topi314/Gopher-Satellite/config/common/koala-base.yaml

substitutions:
  # Phases of the Voice Assistant
  # The voice assistant is ready to be triggered by a wake word
  voice_assist_idle_phase_id: '1'
  # The voice assistant is waiting for a voice command (after being triggered by the wake word)
  voice_assist_waiting_for_command_phase_id: '2'
  # The voice assistant is listening for a voice command
  voice_assist_listening_for_command_phase_id: '3'
  # The voice assistant is currently processing the command
  voice_assist_thinking_phase_id: '4'
  # The voice assistant is replying to the command
  voice_assist_replying_phase_id: '5'
  # The voice assistant is not ready
  voice_assist_not_ready_phase_id: '10'
  # The voice assistant encountered an error
  voice_assist_error_phase_id: '11'

esphome:
  project: 
    name: formatbce.Koala Satellite
    version: 2025.1.3
  name: koala-satellite
  friendly_name: Koala Satellite
  name_add_mac_suffix: true
  min_version: 2024.12.2
  platformio_options:
    board_build.flash_mode: dio
  on_boot:
    priority: 375
    then:
      - sensor.template.publish:
          id: next_timer
          state: -1
      # Run the script to refresh the LED status
      - script.execute: control_leds
      # If after 10 minutes, the device is still initializing (It did not yet connect to Home Assistant), turn off the init_in_progress variable and run the script to refresh the LED status
      - delay: 10min
      - if:
          condition:
            lambda: return id(init_in_progress);
          then:
            - lambda: id(init_in_progress) = false;
            - script.execute: control_leds
  on_shutdown:
    then:
      # Prevent loud noise on software restart
      - lambda: id(respeaker).mute_speaker();

esp32:
  board: esp32-s3-devkitc-1
  variant: esp32s3
  flash_size: 16MB
  framework:
    type: esp-idf
    version: recommended
    sdkconfig_options:
      CONFIG_ESP32S3_DEFAULT_CPU_FREQ_240: "y"
      CONFIG_ESP32S3_DATA_CACHE_64KB: "y"
      CONFIG_ESP32S3_DATA_CACHE_LINE_64B: "y"
      CONFIG_ESP32S3_INSTRUCTION_CACHE_32KB: "y"
      CONFIG_ESP32_S3_BOX_BOARD: "y"
      CONFIG_SPIRAM_ALLOW_STACK_EXTERNAL_MEMORY: "y"

      CONFIG_SPIRAM_TRY_ALLOCATE_WIFI_LWIP: "y"

      # Settings based on https://github.com/espressif/esp-adf/issues/297#issuecomment-783811702
      CONFIG_ESP32_WIFI_STATIC_RX_BUFFER_NUM: "16"
      CONFIG_ESP32_WIFI_DYNAMIC_RX_BUFFER_NUM: "512"
      CONFIG_ESP32_WIFI_STATIC_TX_BUFFER: "y"
      CONFIG_ESP32_WIFI_TX_BUFFER_TYPE: "0"
      CONFIG_ESP32_WIFI_STATIC_TX_BUFFER_NUM: "8"
      CONFIG_ESP32_WIFI_CACHE_TX_BUFFER_NUM: "32"
      CONFIG_ESP32_WIFI_AMPDU_TX_ENABLED: "y"
      CONFIG_ESP32_WIFI_TX_BA_WIN: "16"
      CONFIG_ESP32_WIFI_AMPDU_RX_ENABLED: "y"
      CONFIG_ESP32_WIFI_RX_BA_WIN: "32"
      CONFIG_LWIP_MAX_ACTIVE_TCP: "16"
      CONFIG_LWIP_MAX_LISTENING_TCP: "16"
      CONFIG_TCP_MAXRTX: "12"
      CONFIG_TCP_SYNMAXRTX: "6"
      CONFIG_TCP_MSS: "1436"
      CONFIG_TCP_MSL: "60000"
      CONFIG_TCP_SND_BUF_DEFAULT: "65535"
      CONFIG_TCP_WND_DEFAULT: "65535"  # Adjusted from linked settings to avoid compilation error
      CONFIG_TCP_RECVMBOX_SIZE: "512"
      CONFIG_TCP_QUEUE_OOSEQ: "y"
      CONFIG_TCP_OVERSIZE_MSS: "y"
      CONFIG_LWIP_WND_SCALE: "y"
      CONFIG_TCP_RCV_SCALE: "3"
      CONFIG_LWIP_TCPIP_RECVMBOX_SIZE: "512"

      CONFIG_BT_ALLOCATION_FROM_SPIRAM_FIRST: "y"
      CONFIG_BT_BLE_DYNAMIC_ENV_MEMORY: "y"

      CONFIG_MBEDTLS_EXTERNAL_MEM_ALLOC: "y"
      CONFIG_MBEDTLS_SSL_PROTO_TLS1_3: "y"  # TLS1.3 support isn't enabled by default in IDF 5.1.5

wifi:
  id: wifi_id
  on_connect:
    - lambda: id(improv_ble_in_progress) = false;
    - script.execute: control_leds
  on_disconnect:
    - script.execute: control_leds

logger:
  level: DEBUG
  logs:
    sensor: WARN  # avoids logging debug sensor updates

api:
  id: api_id
  actions:
    - action: start_va
      then:
        - voice_assistant.start
    - action: stop_va
      then:
        - voice_assistant.stop
  on_client_connected:
    - script.execute: control_leds
  on_client_disconnected:
    - script.execute: control_leds

# Uncomment this, if you have problems with text-to-speech because of Home Assistant HTTPS internal URL
# http_request:
#   verify_ssl: false

ota:
  - platform: esphome
    id: ota_esphome

i2c:
  - id: internal_i2c
    sda: GPIO5
    scl: GPIO6
    frequency: 400kHz

psram:
  mode: octal
  speed: 80MHz

globals:
  # Global index for our LEDs. So that switching between different animation does not lead to unwanted effects.
  - id: global_led_animation_index
    type: int
    restore_value: no
    initial_value: '0'
  # Global initialization variable. Initialized to true and set to false once everything is connected. Only used to have a smooth "plugging" experience
  - id: init_in_progress
    type: bool
    restore_value: no
    initial_value: 'true'
  # Global variable storing the state of ImprovBLE. Used to draw different LED animations
  - id: improv_ble_in_progress
    type: bool
    restore_value: no
    initial_value: 'false'
  # Global variable tracking the phase of the voice assistant (defined above). Initialized to not_ready
  - id: voice_assistant_phase
    type: int
    restore_value: no
    initial_value: ${voice_assist_not_ready_phase_id}
  # Global variable tracking if the dial was recently touched.
  - id: dial_touched
    type: bool
    restore_value: no
    initial_value: 'false'
  # Global variable tracking if the LED color was recently changed.
  - id: color_changed
    type: bool
    restore_value: no
    initial_value: 'false'
  # Global variable storing the first active timer
  - id: first_active_timer
    type: voice_assistant::Timer
    restore_value: false
  # Global variable storing if a timer is active
  - id: is_timer_active
    type: bool
    restore_value: false
  # Global variable storing if a factory reset was requested. If it is set to true, the device will factory reset once the center button is released
  - id: factory_reset_requested
    type: bool
    restore_value: no
    initial_value: 'false'

switch:
  # Hardware speaker mute
  - platform: template
    id: speaker_mute_switch
    name: Speaker mute
    icon: mdi:volume-mute
    internal: true
    optimistic: true
    turn_on_action:
      - lambda: id(respeaker).mute_speaker();
    turn_off_action:
      - lambda: id(respeaker).unmute_speaker();
  # stateless momentary mic mute switch
  - platform: gpio
    internal: true
    pin: 
      number: GPIO4 # D3
      inverted: true
    id: mute_toggle
    on_turn_on:
      - delay: 300ms
      - switch.turn_off: mute_toggle
  # stateful user facing mic mute switch
  - platform: template
    id: mic_mute_switch
    name: Mic mute
    icon: mdi:microphone-off
    lambda: |-
      if (id(mute_state).state) {
        return true;
      } else {
        return false;
      }
    on_turn_on:
      - if:
          condition:
            and:
              - lambda: return !id(init_in_progress);
              - switch.is_on: mute_sound
          then:
            - script.execute:
                id: play_sound
                priority: false
                sound_file: !lambda return id(mute_switch_on_sound);
    on_turn_off:
      - if:
          condition:
            and:
              - lambda: return !id(init_in_progress);
              - switch.is_on: mute_sound
          then:
            - script.execute:
                id: play_sound
                priority: false
                sound_file: !lambda return id(mute_switch_off_sound);
    turn_on_action:
      - switch.turn_on: mute_toggle
    turn_off_action:
      - switch.turn_on: mute_toggle
  # Button click Sounds Switch.
  - platform: template
    id: button_sound
    name: Button click sounds
    icon: "mdi:bullhorn"
    entity_category: config
    optimistic: true
    restore_mode: RESTORE_DEFAULT_ON
  # Mute Sound Switch.
  - platform: template
    id: mute_sound
    name: Mute/unmute sound
    icon: "mdi:bullhorn"
    entity_category: config
    optimistic: true
    restore_mode: RESTORE_DEFAULT_ON
  # Wake Word Sound Switch.
  - platform: template
    id: wake_sound
    name: Wake sound
    icon: "mdi:bullhorn"
    entity_category: config
    optimistic: true
    restore_mode: RESTORE_DEFAULT_ON
  # Internal switch to track when a timer is ringing on the device.
  - platform: template
    id: timer_ringing
    optimistic: true
    internal: true
    restore_mode: ALWAYS_OFF
    on_turn_off:
      # Disable stop wake word
      - lambda: id(stop).disable();
      # Stop any current annoucement (ie: stop the timer ring mid playback)
      - if:
          condition:
            lambda: return id(nabu_media_player)->state == media_player::MediaPlayerState::MEDIA_PLAYER_STATE_ANNOUNCING;
          then:
            lambda: |-
              id(nabu_media_player)
                ->make_call()
                .set_command(media_player::MediaPlayerCommand::MEDIA_PLAYER_COMMAND_STOP)
                .set_announcement(true)
                .perform();
      # Set back ducking ratio to zero
      - nabu.set_ducking:
          decibel_reduction: 0
          duration: 1.0s
      # Refresh the LED ring
      - script.execute: control_leds
    on_turn_on:
      # Duck audio
      - nabu.set_ducking:
          decibel_reduction: 20
          duration: 0.0s
      # Enable stop wake word
      - lambda: id(stop).enable();
      # Ring timer
      - script.execute: ring_timer
      # Refresh LED
      - script.execute: control_leds
      # If 15 minutes have passed and the timer is still ringing, stop it.
      - delay: 15min
      - switch.turn_off: timer_ringing

binary_sensor:
  # User Button. Used for many things (See on_multi_click)
  - platform: gpio
    id: user_button
    pin:
      number: GPIO42
      inverted: true
    name: "User button"
    on_press:
      - script.execute: control_leds
    on_release:
      - script.execute: control_leds
      # If a factory reset is requested, factory reset on release
      - if:
          condition:
            lambda: return id(factory_reset_requested);
          then:
            - button.press: factory_reset_button
    on_multi_click:
      # Simple Click:
      #   - Abort "things" in order
      #     - Timer
      #     - Announcements
      #     - Voice Assistant Pipeline run
      #     - Music
      #   - Starts the voice assistant if it is not yet running and if the device is not muted.
      - timing:
          - ON for at most 1s
          - OFF for at least 0.25s
        then:
          - if:
              condition:
                lambda: return !id(init_in_progress) && !id(color_changed);
              then:
                - if:
                    condition:
                      switch.is_on: timer_ringing
                    then:
                      - switch.turn_off: timer_ringing
                    else:
                      - if:
                          condition:
                            lambda: return id(nabu_media_player)->state == media_player::MediaPlayerState::MEDIA_PLAYER_STATE_ANNOUNCING;
                          then:
                            - lambda: |
                                id(nabu_media_player)
                                  ->make_call()
                                  .set_command(media_player::MediaPlayerCommand::MEDIA_PLAYER_COMMAND_STOP)
                                  .set_announcement(true)
                                  .perform();
                          else:
                            - if:
                                condition:
                                  voice_assistant.is_running:
                                then:
                                  - voice_assistant.stop:
                                else:
                                  - if:
                                      condition:
                                        media_player.is_playing:
                                      then:
                                        - media_player.pause:
                                      else:
                                        - if:
                                            condition:
                                              and:
                                                - switch.is_off: mic_mute_switch
                                                - not:
                                                    voice_assistant.is_running
                                            then:
                                              - if:
                                                  condition:
                                                    switch.is_on: button_sound
                                                  then:
                                                    - script.execute:
                                                        id: play_sound
                                                        priority: true
                                                        sound_file: !lambda return id(center_button_press_sound);
                                                    - delay: 300ms
                                              - voice_assistant.start:
      # Double Click
      #  . Exposed as an event entity. To be used in automations inside Home Assistant
      - timing:
          - ON for at most 1s
          - OFF for at most 0.25s
          - ON for at most 1s
          - OFF for at least 0.25s
        then:
          - if:
              condition:
                lambda: return !id(init_in_progress) && !id(color_changed);
              then:
                - if:
                    condition:
                      switch.is_on: button_sound
                    then:
                      - script.execute:
                          id: play_sound
                          priority: false
                          sound_file: !lambda return id(center_button_double_press_sound);
                - event.trigger:
                    id: button_press_event
                    event_type: "double_press"
      # Triple Click
      #  . Exposed as an event entity. To be used in automations inside Home Assistant
      - timing:
          - ON for at most 1s
          - OFF for at most 0.25s
          - ON for at most 1s
          - OFF for at most 0.25s
          - ON for at most 1s
          - OFF for at least 0.25s
        then:
          - if:
              condition:
                lambda: return !id(init_in_progress) && !id(color_changed);
              then:
                - if:
                    condition:
                      switch.is_on: button_sound
                    then:
                      - script.execute:
                          id: play_sound
                          priority: false
                          sound_file: !lambda return id(center_button_triple_press_sound);
                - event.trigger:
                    id: button_press_event
                    event_type: "triple_press"
      # Long Press
      #  . Exposed as an event entity. To be used in automations inside Home Assistant
      - timing:
          - ON for at least 1s
        then:
          - if:
              condition:
                lambda: return !id(init_in_progress) && !id(color_changed);
              then:
                - if:
                    condition:
                      switch.is_on: button_sound
                    then:
                      - script.execute:
                          id: play_sound
                          priority: false
                          sound_file: !lambda return id(center_button_long_press_sound);
                - light.turn_off: voice_assistant_leds
                - event.trigger:
                    id: button_press_event
                    event_type: "long_press"
      # Factory Reset Warning
      #  . Audible and Visible warning.
      - timing:
          - ON for at least 10s
        then:
          - if:
              condition:
                lambda: return !id(dial_touched);
              then:
                - light.turn_on:
                    brightness: 100%
                    id: voice_assistant_leds
                    effect: "Factory Reset Coming Up"
                - script.execute:
                    id: play_sound
                    priority: true
                    sound_file: !lambda return id(factory_reset_initiated_sound);
                - wait_until:
                    binary_sensor.is_off: user_button
                - if:
                    condition:
                      lambda: return !id(factory_reset_requested);
                    then:
                      - light.turn_off: voice_assistant_leds
                      - script.execute:
                          id: play_sound
                          priority: true
                          sound_file: !lambda return id(factory_reset_cancelled_sound);
      # Factory Reset Confirmed.
      #  . Audible warning to prompt user to release the button
      #  . Set factory_reset_requested to true
      - timing:
          - ON for at least 22s
        then:
          - if:
              condition:
                lambda: return !id(dial_touched);
              then:
                - script.execute:
                    id: play_sound
                    priority: true
                    sound_file: !lambda return id(factory_reset_confirmed_sound);
                - light.turn_on:
                    brightness: 100%
                    red: 100%
                    green: 0%
                    blue: 0%
                    id: voice_assistant_leds
                    effect: "none"
                - lambda: id(factory_reset_requested) = true;

  - platform: gpio
  # this thing is pretty flaky, giving several on/off commands at once. Do not use it for serious stuff
    id: rotary_button
    disabled_by_default: true
    pin:
      number: GPIO20
      inverted: true
      mode:
        input: true
        pullup: true

light:
  # Hardware LED ring. Not used because remapping needed
  - platform: esp32_rmt_led_strip
    id: leds_internal
    pin: GPIO13
    rmt_channel: 1
    num_leds: 43
    rgb_order: GRB
    chipset: WS2812
    default_transition_length: 0ms

  # Voice Assistant LED ring. Remapping of the internal LED.
  # This light is not exposed. The device controls it
  - platform: partition
    id: voice_assistant_leds
    internal: true
    default_transition_length: 0ms
    segments:
      - id: leds_internal
        from: 0
        to: 31
        reversed: True
      - id: leds_internal
        from: 32
        to: 42
        reversed: True
    effects:
      - addressable_lambda:
          name: "Waiting for Command"
          update_interval: 100ms
          lambda: |-
            auto light_color = id(led_ring).current_values;
            Color color(light_color.get_red() * 255, light_color.get_green() * 255,
                  light_color.get_blue() * 255);
            for (int i = 0; i < 43; i++) {
              if (i % 6 == id(global_led_animation_index) % 6) {
                it[i] = color;
              } else if ((i + 5) % 6 == id(global_led_animation_index) % 6) {
                it[i] = color * 192;
              } else if ((i + 4) % 6 == id(global_led_animation_index) % 6) {
                it[i] = color * 128;
              } else {
                it[i] = Color::BLACK;
              }
            }
            id(global_led_animation_index) = (id(global_led_animation_index) + 1) % 43;
      - addressable_lambda:
          name: "Listening For Command"
          update_interval: 50ms
          lambda: |-
            auto light_color = id(led_ring).current_values;
            Color color(light_color.get_red() * 255, light_color.get_green() * 255, light_color.get_blue() * 255);
            for (int i = 0; i < 43; i++) {
              if (i % 6 == id(global_led_animation_index) % 6) {
                it[i] = color;
              } else if ((i + 5) % 6 == id(global_led_animation_index) % 6) {
                it[i] = color * 192;
              } else if ((i + 4) % 6 == id(global_led_animation_index) % 6) {
                it[i] = color * 128;
              } else {
                it[i] = Color::BLACK;
              }
            }
            id(global_led_animation_index) = (id(global_led_animation_index) + 1) % 43;
      - addressable_lambda:
          name: "Thinking"
          update_interval: 10ms
          lambda: |-
            static uint8_t brightness_step = 0;
            static bool brightness_decreasing = true;
            static uint8_t brightness_step_number = 10;
            if (initial_run) {
              brightness_step = 0;
              brightness_decreasing = true;
            }
            auto light_color = id(led_ring).current_values;
            Color color(light_color.get_red() * 255, light_color.get_green() * 255, light_color.get_blue() * 255);
            for (int i = 0; i < 43; i++) {
              if (i % 6 == id(global_led_animation_index) % 6) {
                it[i] = color * uint8_t(255/brightness_step_number*(brightness_step_number-brightness_step));
              } else {
                it[i] = Color::BLACK;
              }
            }
            if (brightness_decreasing) {
              brightness_step++;
            } else {
              brightness_step--;
            }
            if (brightness_step == 0 || brightness_step == brightness_step_number) {
              brightness_decreasing = !brightness_decreasing;
            }
      - addressable_lambda:
          name: "Replying"
          update_interval: 50ms
          lambda: |-
            id(global_led_animation_index) = (43 + id(global_led_animation_index) - 1) % 43;
            auto light_color = id(led_ring).current_values;
            Color color(light_color.get_red() * 255, light_color.get_green() * 255, light_color.get_blue() * 255);
            for (int i = 0; i < 43; i++) {
              if (i % 6 == id(global_led_animation_index) % 6) {
                it[i] = color;
              } else if ((i + 1) % 6 == id(global_led_animation_index) % 6) {
                it[i] = color * 192;
              } else if ((i + 2) % 6 == id(global_led_animation_index) % 6) {
                it[i] = color * 128;
              } else {
                it[i] = Color::BLACK;
              }
            }
      - addressable_lambda:
          name: "Volume Display"
          update_interval: 50ms
          lambda: |-
            Color color(255, 0, 255);
            Color silenced_color(255, 0, 0);
            auto volume_ratio = id(nabu_media_player).volume * 10.0f;
            auto is_muted = id(nabu_media_player).is_muted() || id(nabu_media_player).volume == 0.0f;
            for (int i = 0; i < 43; i++) {
              if (i <= volume_ratio && !is_muted) {
                it[i] = color * min( 255.0f * (volume_ratio - i) , 255.0f ) ;
              } else {
                it[i] = Color::BLACK;
              }
            }
            if (is_muted) {
              it[5] = silenced_color;
            }
      - addressable_lambda:
          name: "Center Button Touched"
          update_interval: 16ms
          lambda: |-
            if (initial_run) {
              // set voice_assistant_leds light to colors based on led_ring
              auto led_ring_cv = id(led_ring).current_values;
              auto va_leds_call = id(voice_assistant_leds).make_call();
              va_leds_call.from_light_color_values(led_ring_cv);
              va_leds_call.set_brightness( min ( max( id(led_ring).current_values.get_brightness() , 0.2f ) + 0.1f , 1.0f ) );
              va_leds_call.set_state(true);
              va_leds_call.perform();
            }
            auto light_color = id(voice_assistant_leds).current_values;
            Color color(light_color.get_red() * 255, light_color.get_green() * 255,
                  light_color.get_blue() * 255);
            for (int i = 0; i < 43; i++) {
              it[i] = color;
            }
      - addressable_twinkle:
          name: "Twinkle"
          twinkle_probability: 50%
      - addressable_rainbow:
          name: "Rainbow"
          width: 43
      - addressable_lambda:
          name: "Error"
          update_interval: 10ms
          lambda: |-
            static uint8_t brightness_step = 0;
            static bool brightness_decreasing = true;
            static uint8_t brightness_step_number = 10;
            if (initial_run) {
              brightness_step = 0;
              brightness_decreasing = true;
            }
            Color error_color(255, 0, 0);
            for (int i = 0; i < 43; i++) {
              it[i] = error_color * uint8_t(255/brightness_step_number*(brightness_step_number-brightness_step));
            }
            if (brightness_decreasing) {
              brightness_step++;
            } else {
              brightness_step--;
            }
            if (brightness_step == 0 || brightness_step == brightness_step_number) {
              brightness_decreasing = !brightness_decreasing;
            }
      - addressable_lambda:
          name: "Timer Ring"
          update_interval: 10ms
          lambda: |-
            static uint8_t brightness_step = 0;
            static bool brightness_decreasing = true;
            static uint8_t brightness_step_number = 10;
            if (initial_run) {
              brightness_step = 0;
              brightness_decreasing = true;
            }
            auto light_color = id(led_ring).current_values;
            Color color(light_color.get_red() * 255, light_color.get_green() * 255,
                  light_color.get_blue() * 255);
            for (int i = 0; i < 43; i++) {
              it[i] = color * uint8_t(255/brightness_step_number*(brightness_step_number-brightness_step));
            }
            if (brightness_decreasing) {
              brightness_step++;
            } else {
              brightness_step--;
            }
            if (brightness_step == 0 || brightness_step == brightness_step_number) {
              brightness_decreasing = !brightness_decreasing;
            }
      - addressable_lambda:
          name: "Timer Tick"
          update_interval: 100ms
          lambda: |-
            auto light_color = id(led_ring).current_values;
            Color color(light_color.get_red() * 255, light_color.get_green() * 255,
                  light_color.get_blue() * 255);
            auto timer_ratio = 43.0f * id(first_active_timer).seconds_left / max(id(first_active_timer).total_seconds , static_cast<uint32_t>(1));
            uint8_t last_led_on = static_cast<uint8_t>(ceil(timer_ratio)) - 1;
            for (int i = 0; i < 43; i++) {
              float brightness_dip = ( i == id(global_led_animation_index) % 43 && i != last_led_on ) ? 0.96f : 1.0f ;
              if (i <= timer_ratio) {
                it[i] = color * min(255.0f * brightness_dip * (timer_ratio - i) , 255.0f * brightness_dip) ;
              } else {
                it[i] = Color::BLACK;
              }
            }
            id(global_led_animation_index) = (43 + id(global_led_animation_index) - 1) % 43;
      - addressable_lambda:
          name: "Factory Reset Coming Up"
          update_interval: 1s
          lambda: |-
            static uint8_t index = 0;
            Color color(255, 0, 0);
            if (initial_run) {
              index = 0;
            }
            for (int i = 0; i < 43; i++) {
              if (i <= index ) {
                it[i] = color;
              } else {
                it[i] = Color::BLACK;
              }
            }
            index = (index + 1) % 43;
  # User facing LED ring. Remapping of the internal LEDs.
  # Exposed to be used by the user.
  - platform: partition
    id: led_ring
    name: LED Ring
    entity_category: config
    icon: "mdi:circle-outline"
    default_transition_length: 0ms
    restore_mode: RESTORE_DEFAULT_OFF
    initial_state:
      color_mode: rgb
      brightness: 66%
      red: 9.4%
      green: 73.3%
      blue: 94.9%
    segments:
      - id: leds_internal
        from: 0
        to: 31
        reversed: True
      - id: leds_internal
        from: 32
        to: 42
        reversed: True
    effects:
      - addressable_rainbow:
          name: "Rainbow"
          width: 43

  - platform: esp32_rmt_led_strip
    id: led_respeaker_onboard
    name: LED Respeaker onboard
    disabled_by_default: true
    internal: false
    rgb_order: GRB
    pin: GPIO1
    num_leds: 1
    rmt_channel: 2
    chipset: ws2812
    entity_category: config
    default_transition_length: 0s
    effects:
      - pulse:
          name: "Fast Pulse"
          transition_length: 100ms
          update_interval: 100ms
          min_brightness: 50%
          max_brightness: 100%
      - pulse:
          name: "Slow Pulse"
          transition_length: 500ms
          update_interval: 500ms
          min_brightness: 50%
          max_brightness: 100%
  - platform: esp32_rmt_led_strip
    id: led_esp_onboard
    name: LED ESP onboard
    disabled_by_default: true
    internal: false
    rgb_order: GRB
    pin: GPIO48
    num_leds: 1
    rmt_channel: 0
    chipset: ws2812
    entity_category: config
    default_transition_length: 0s

sensor:
  # The dial. Used to control volume and Hue of the LED ring.
  - platform: rotary_encoder
    id: dial
    pin_a: GPIO47
    pin_b: GPIO21
    resolution: 2
    on_clockwise:
      - lambda: id(dial_touched) = true;
      - if:
          condition:
            binary_sensor.is_off: user_button
          then:
            - script.execute:
                id: control_volume
                increase_volume: true
          else:
            - script.execute:
                id: control_hue
                increase_hue: true
    on_anticlockwise:
      - lambda: id(dial_touched) = true;
      - if:
          condition:
            binary_sensor.is_off: user_button
          then:
            - script.execute:
                id: control_volume
                increase_volume: false
          else:
            - script.execute:
                id: control_hue
                increase_hue: false
  - platform: template
    id: next_timer
    name: "Next timer"
    update_interval: never
    disabled_by_default: true
    device_class: duration
    unit_of_measurement: s
    icon: "mdi:timer"

text_sensor:
  - platform: template
    id: next_timer_name
    name: "Next timer name"
    icon: "mdi:timer"
    disabled_by_default: true
  - platform: template
    id: tts_uri
    name: "TTS URI"
    disabled_by_default: true

event:
  # Event entity exposed to the user to automate on complex center button presses.
  # The simple press is not exposed as it is used to control the device itself.
  - platform: template
    id: button_press_event
    name: "Button press"
    icon: mdi:button-pointer
    device_class: button
    event_types:
      - double_press
      - triple_press
      - long_press

script:
  # Master script controlling the LEDs, based on different conditions : initialization in progress, wifi and api connected and voice assistant phase.
  # For the sake of simplicity and re-usability, the script calls child scripts defined below.
  # This script will be called every time one of these conditions is changing.
  - id: control_leds
    then:
      - lambda: |
          id(check_if_timers_active).execute();
          if (id(is_timer_active)){
            id(fetch_first_active_timer).execute();
          }
          if (id(improv_ble_in_progress)) {
            id(control_leds_improv_ble_state).execute();
          } else if (id(init_in_progress)) {
            id(control_leds_init_state).execute();
          } else if (!id(wifi_id).is_connected() || !id(api_id).is_connected()){
            id(control_leds_no_ha_connection_state).execute();
          } else if (id(user_button).state) {
            id(control_leds_center_button_touched).execute();
          } else if (id(dial_touched)) {
            id(control_leds_volume_changed).execute();
          } else if (id(timer_ringing).state) {
            id(control_leds_timer_ringing).execute();
          } else if (id(voice_assistant_phase) == ${voice_assist_waiting_for_command_phase_id}) {
            id(control_leds_voice_assistant_waiting_for_command_phase).execute();
          } else if (id(voice_assistant_phase) == ${voice_assist_listening_for_command_phase_id}) {
            id(control_leds_voice_assistant_listening_for_command_phase).execute();
          } else if (id(voice_assistant_phase) == ${voice_assist_thinking_phase_id}) {
            id(control_leds_voice_assistant_thinking_phase).execute();
          } else if (id(voice_assistant_phase) == ${voice_assist_replying_phase_id}) {
            id(control_leds_voice_assistant_replying_phase).execute();
          } else if (id(voice_assistant_phase) == ${voice_assist_error_phase_id}) {
            id(control_leds_voice_assistant_error_phase).execute();
          } else if (id(voice_assistant_phase) == ${voice_assist_not_ready_phase_id}) {
            id(control_leds_voice_assistant_not_ready_phase).execute();
          } else if (id(is_timer_active)) {
            id(control_leds_timer_ticking).execute();
          } else if (id(voice_assistant_phase) == ${voice_assist_idle_phase_id}) {
            id(control_leds_voice_assistant_idle_phase).execute();
          }

  # Script executed during Improv BLE
  # Warm White Twinkle
  - id: control_leds_improv_ble_state
    then:
      - light.turn_on:
          brightness: 50%
          red: 100%
          green: 89%
          blue: 71%
          id: voice_assistant_leds
          effect: "Twinkle"

  # Script executed during initialization
  # Blue Twinkle if Wifi is connected, Else rainbow
  - id: control_leds_init_state
    then:
      - if:
          condition:
            wifi.connected:
          then:
            - light.turn_on:
                brightness: 50%
                red: 9.4%
                green: 73.3%
                blue: 94.9%
                id: voice_assistant_leds
                effect: "Twinkle"
          else:
            - light.turn_on:
                id: voice_assistant_leds
                effect: "Rainbow"

  # Script executed when the device has no connection to Home Assistant
  # Red Twinkle (This will be visible during HA updates for example)
  - id: control_leds_no_ha_connection_state
    then:
      - light.turn_on:
          brightness: 50%
          red: 1
          green: 0
          blue: 0
          id: voice_assistant_leds
          effect: "Twinkle"

  # Script executed when the voice assistant is idle (waiting for a wake word)
  # Nothing (Either LED ring off or LED ring on if the user decided to turn the user facing LED ring on)
  - id: control_leds_voice_assistant_idle_phase
    then:
      - light.turn_off: voice_assistant_leds
      - if:
          condition:
            light.is_on: led_ring
          then:
            light.turn_on: led_ring

  # Script executed when the voice assistant is waiting for a command (After the wake word)
  # Slow clockwise spin of the LED ring.
  - id: control_leds_voice_assistant_waiting_for_command_phase
    then:
      - light.turn_on:
          brightness: !lambda return max( id(led_ring).current_values.get_brightness() , 0.2f );
          id: voice_assistant_leds
          effect: "Waiting for Command"

  # Script executed when the voice assistant is listening to a command
  # Fast clockwise spin of the LED ring.
  - id: control_leds_voice_assistant_listening_for_command_phase
    then:
      - light.turn_on:
          brightness: !lambda return max( id(led_ring).current_values.get_brightness() , 0.2f );
          id: voice_assistant_leds
          effect: "Listening For Command"

  # Script executed when the voice assistant is thinking to a command
  # The spin stops and the 2 LEDs that are currently on and blinking indicating the commend is being processed.
  - id: control_leds_voice_assistant_thinking_phase
    then:
      - light.turn_on:
          brightness: !lambda return max( id(led_ring).current_values.get_brightness() , 0.2f );
          id: voice_assistant_leds
          effect: "Thinking"

  # Script executed when the voice assistant is replying to a command
  # Fast anticlockwise spin of the LED ring.
  - id: control_leds_voice_assistant_replying_phase
    then:
      - light.turn_on:
          brightness: !lambda return max( id(led_ring).current_values.get_brightness() , 0.2f );
          id: voice_assistant_leds
          effect: "Replying"

  # Script executed when the voice assistant is in error
  # Fast Red Pulse
  - id: control_leds_voice_assistant_error_phase
    then:
      - light.turn_on:
          brightness: !lambda return min ( max( id(led_ring).current_values.get_brightness() , 0.2f ) + 0.1f , 1.0f );
          red: 1
          green: 0
          blue: 0
          id: voice_assistant_leds
          effect: "Error"

  # Script executed when the voice assistant is not ready
  - id: control_leds_voice_assistant_not_ready_phase
    then:
      - light.turn_on:
          brightness: 66%
          red: 1
          green: 0
          blue: 0
          id: voice_assistant_leds
          effect: "Twinkle"

  # Script executed when the volume is changed
  # A number of LEDs turn on indicating a visual representation of the volume of the media player entity.
  - id: control_leds_volume_changed
    mode: restart
    then:
      - light.turn_on:
          brightness: !lambda return max( id(led_ring).current_values.get_brightness() , 0.2f );
          id: voice_assistant_leds
          effect: "Volume Display"
      - delay: 2s
      - script.execute: control_leds

  # Script executed when the center button is touched
  # The complete LED ring turns on
  - id: control_leds_center_button_touched
    then:
      - light.turn_on:
          brightness: !lambda return min ( max( id(led_ring).current_values.get_brightness() , 0.2f ) + 0.1f , 1.0f );
          id: voice_assistant_leds
          effect: "Center Button Touched"

  # Script executed when the timer is ringing, to control the LEDs
  # The LED ring blinks.
  - id: control_leds_timer_ringing
    then:
      - light.turn_on:
          brightness: !lambda return min ( max( id(led_ring).current_values.get_brightness() , 0.2f ) + 0.1f , 1.0f );
          id: voice_assistant_leds
          effect: "Timer Ring"

  # Script executed when the timer is ticking, to control the LEDs
  # The LEDs shows the remaining time as a fraction of the full ring.
  - id: control_leds_timer_ticking
    then:
      - light.turn_on:
          brightness: !lambda return max( id(led_ring).current_values.get_brightness() , 0.2f );
          id: voice_assistant_leds
          effect: "Timer tick"

  # Script executed when the volume is increased/decreased from the dial
  - id: control_volume
    mode: restart
    parameters:
      increase_volume: bool  # True: Increase volume / False: Decrease volume.
    then:
      - delay: 16ms
      - if:
          condition:
            lambda: return increase_volume;
          then:
            - media_player.volume_up:
          else:
            - media_player.volume_down:
      - script.execute: control_leds
      - delay: 1s
      - lambda: id(dial_touched) = false;
      - sensor.rotary_encoder.set_value:
          id: dial
          value: 0
      - script.execute: control_leds

  # Script executed when the hue is increased/decreased from the dial
  - id: control_hue
    mode: restart
    parameters:
      increase_hue: bool  # True: Increase hue / False: Decrease hue.
    then:
      - delay: 16ms
      - if:
          condition:
            lambda: return(abs(int(id(dial).state)) > 3 || id(color_changed));
          then:
            - lambda: |
                id(color_changed) = true;
                auto light_color = id(voice_assistant_leds).current_values;
                int hue = 0;
                float saturation = 0;
                float value = 0;
                rgb_to_hsv( light_color.get_red(),
                            light_color.get_green(),
                            light_color.get_blue(),
                            hue,
                            saturation,
                            value);
                if (increase_hue) {
                  hue = (hue + 10) % 360;
                } else {
                  hue = (hue + 350) % 360;
                }
                if (saturation < 0.05) {
                  saturation = 1;
                }
                float red = 0;
                float green = 0;
                float blue = 0;
                hsv_to_rgb( hue,
                            saturation,
                            value,
                            red,
                            green,
                            blue);
                id(voice_assistant_leds).make_call().set_rgb(red, green, blue).perform();
      - script.execute: control_leds
      - wait_until:
          binary_sensor.is_off: user_button
      - lambda: |
          id(dial_touched) = false;
          // now we "save" the new LED color/state to led_ring, maintaining its brightness and state
          auto led_ring_call = id(led_ring).make_call();
          auto va_leds_cv = id(voice_assistant_leds).current_values;
          led_ring_call.from_light_color_values(va_leds_cv);
          led_ring_call.set_brightness(id(led_ring).current_values.get_brightness());
          led_ring_call.set_state(id(led_ring).current_values.is_on());
          led_ring_call.perform();
      - sensor.rotary_encoder.set_value:
          id: dial
          value: 0
      - script.execute: control_leds
      - delay: 500ms
      - lambda: id(color_changed) = false;

  # Script executed when the timer is ringing, to playback sounds.
  - id: ring_timer
    then:
      - while:
          condition:
            switch.is_on: timer_ringing
          then:
            - script.execute:
                id: play_sound
                priority: true
                sound_file: !lambda return id(timer_finished_sound);
            - wait_until:
                lambda: |-
                  return id(nabu_media_player)->state == media_player::MediaPlayerState::MEDIA_PLAYER_STATE_ANNOUNCING;
            - wait_until:
                not:
                  lambda: |-
                    return id(nabu_media_player)->state == media_player::MediaPlayerState::MEDIA_PLAYER_STATE_ANNOUNCING;

  # Script executed when we want to play sounds on the device.
  - id: play_sound
    parameters:
      priority: bool
      sound_file: "media_player::MediaFile*"
    then:
      - lambda: |-
          if (priority) {
            id(nabu_media_player)
              ->make_call()
              .set_command(media_player::MediaPlayerCommand::MEDIA_PLAYER_COMMAND_STOP)
              .set_announcement(true)
              .perform();
          }
          if ( (id(nabu_media_player).state != media_player::MediaPlayerState::MEDIA_PLAYER_STATE_ANNOUNCING ) || priority) {
            id(nabu_media_player)
              ->make_call()
              .set_announcement(true)
              .set_local_media_file(sound_file)
              .perform();
          }

  # Script used to fetch the first active timer (Stored in global first_active_timer)
  - id: fetch_first_active_timer
    then:
      - lambda: |
          const auto timers = id(va).get_timers();
          auto output_timer = timers.begin()->second;
          for (auto &iterable_timer : timers) {
            if (iterable_timer.second.is_active && iterable_timer.second.seconds_left <= output_timer.seconds_left) {
              output_timer = iterable_timer.second;
            }
          }
          id(first_active_timer) = output_timer;

  # Script used to check if a timer is active (Stored in global is_timer_active)
  - id: check_if_timers_active
    then:
      - lambda: |
          const auto timers = id(va).get_timers();
          bool output = false;
          if (timers.size() > 0) {
            for (auto &iterable_timer : timers) {
              if(iterable_timer.second.is_active) {
                output = true;
              }
            }
          }
          id(is_timer_active) = output;

  # Script used activate the stop word if the TTS step is long.
  # Why is this wrapped on a script?
  #   Becasue we want to stop the sequence if the TTS step is faster than that.
  #   This allows us to prevent having the deactivation of the stop word before its own activation.
  - id: activate_stop_word_if_tts_step_is_long
    then:
      - delay: 1s
      # Enable stop wake word
      - lambda: id(stop).enable();

i2s_audio:
  - id: i2s_output
    i2s_lrclk_pin: 
      number: GPIO7
      allow_other_uses: true
    i2s_bclk_pin:  
      number: GPIO8
      allow_other_uses: true
    i2s_mclk_pin:  
      number: GPIO9
      allow_other_uses: true

  - id: i2s_input
    i2s_lrclk_pin:  
      number: GPIO7
      allow_other_uses: true
    i2s_bclk_pin:  
      number: GPIO8
      allow_other_uses: true
    i2s_mclk_pin:  
      number: GPIO9
      allow_other_uses: true

microphone:
  - platform: nabu_microphone
    i2s_din_pin: GPIO44
    adc_type: external
    pdm: false
    sample_rate: 48000
    bits_per_sample: 32bit
    i2s_mode: secondary
    i2s_audio_id: i2s_input
    channel_0:
      id: nabu_mic_mww
    channel_1:
      id: nabu_mic_va
      
speaker:
  - platform: i2s_audio
    sample_rate: 48000
    i2s_mode: secondary
    i2s_dout_pin: GPIO43
    bits_per_sample: 32bit
    i2s_audio_id: i2s_output
    dac_type: external
    channel: stereo
    timeout: never
    buffer_duration: 100ms

media_player:
  - platform: nabu
    id: nabu_media_player
    name: Media Player
    internal: false
    audio_dac:
    speaker:
    sample_rate: 48000
    volume_increment: 0.05
    volume_min: 0.4
    volume_max: 0.85
    on_mute:
      - script.execute: control_leds_volume_changed
    on_unmute:
      - script.execute: control_leds_volume_changed
    on_volume:
      - script.execute: control_leds_volume_changed
    on_announcement:
      - nabu.set_ducking:
          decibel_reduction: 20
          duration: 0.0s
    on_state:
      if:
        condition:
          and:
            - switch.is_off: timer_ringing
            - not:
                voice_assistant.is_running:
            - not:
                lambda: return id(nabu_media_player)->state == media_player::MediaPlayerState::MEDIA_PLAYER_STATE_ANNOUNCING;
        then:
          - nabu.set_ducking:
              decibel_reduction: 0
              duration: 1.0s
    files:
      - id: center_button_press_sound
        file: https://github.com/esphome/home-assistant-voice-pe/raw/dev/sounds/center_button_press.flac
      - id: center_button_double_press_sound
        file: https://github.com/esphome/home-assistant-voice-pe/raw/dev/sounds/center_button_double_press.flac
      - id: center_button_triple_press_sound
        file: https://github.com/esphome/home-assistant-voice-pe/raw/dev/sounds/center_button_triple_press.flac
      - id: center_button_long_press_sound
        file: https://github.com/esphome/home-assistant-voice-pe/raw/dev/sounds/center_button_long_press.flac
      - id: factory_reset_initiated_sound
        file: https://github.com/esphome/home-assistant-voice-pe/raw/dev/sounds/factory_reset_initiated.mp3
      - id: factory_reset_cancelled_sound
        file: https://github.com/esphome/home-assistant-voice-pe/raw/dev/sounds/factory_reset_cancelled.mp3
      - id: factory_reset_confirmed_sound
        file: https://github.com/esphome/home-assistant-voice-pe/raw/dev/sounds/factory_reset_confirmed.mp3
      - id: mute_switch_on_sound
        file: https://github.com/esphome/home-assistant-voice-pe/raw/dev/sounds/mute_switch_on.flac
      - id: mute_switch_off_sound
        file: https://github.com/esphome/home-assistant-voice-pe/raw/dev/sounds/mute_switch_off.flac
      - id: timer_finished_sound
        file: https://github.com/esphome/home-assistant-voice-pe/raw/dev/sounds/timer_finished.flac
      - id: wake_word_triggered_sound
        file: https://github.com/esphome/home-assistant-voice-pe/raw/dev/sounds/wake_word_triggered.flac

respeaker_lite:
  id: respeaker
  reset_pin: GPIO2
  mute_state:
    internal: true
    id: mute_state
  firmware_version:
    icon: mdi:application-cog
    name: XMOS firmware version
    internal: false
    id: firmware_version

external_components:
  - source:
      type: git
      url: https://github.com/esphome/home-assistant-voice-pe
      ref: dev
    components:
      - aic3204
      - audio_dac
      - media_player
      - micro_wake_word
      - microphone
      - nabu
      - voice_assistant
    refresh: 0s
  - source:
      type: git
      url: https://github.com/formatBCE/home-assistant-voice-pe
      ref: 48kHz_mic_support
    components:
      - nabu_microphone
    refresh: 0s
  - source:
      type: git
      url: https://github.com/formatBCE/Respeaker-Lite-ESPHome-integration
      ref: main
    components: 
      - respeaker_lite
    refresh: 0s
  - source: github://pr#8018
    components: [http_request]
    refresh: 0s

audio_dac:
  - platform: aic3204
    i2c_id: internal_i2c

micro_wake_word:
  id: mww
  models:
    - model: https://github.com/kahrendt/microWakeWord/releases/download/okay_nabu_20241223.2/okay_nabu.json
      # Use this to adjust sensitivity for the wake word
      # probability_cutoff: 0.8
      id: okay_nabu
    - model: hey_jarvis
      id: hey_jarvis
    - model: hey_mycroft
      id: hey_mycroft
    - model: https://github.com/kahrendt/microWakeWord/releases/download/stop/stop.json
      id: stop
      internal: true
  vad:
  microphone: nabu_mic_mww
  on_wake_word_detected:
    # If the wake word is detected when the device is muted (Possible with the software mute switch): Do nothing
    - if:
        condition:
          switch.is_off: mic_mute_switch
        then:
          # If a timer is ringing: Stop it, do not start the voice assistant (We can stop timer from voice!)
          - if:
              condition:
                switch.is_on: timer_ringing
              then:
                - switch.turn_off: timer_ringing
              # Start voice assistant, stop current announcement.
              else:
                - if:
                    condition:
                      lambda: return id(nabu_media_player)->state == media_player::MediaPlayerState::MEDIA_PLAYER_STATE_ANNOUNCING;
                    then:
                      lambda: |-
                        id(nabu_media_player)
                          ->make_call()
                          .set_command(media_player::MediaPlayerCommand::MEDIA_PLAYER_COMMAND_STOP)
                          .set_announcement(true)
                          .perform();
                    else:
                      - if:
                          condition:
                            switch.is_on: wake_sound
                          then:
                            - script.execute:
                                id: play_sound
                                priority: true
                                sound_file: !lambda return id(wake_word_triggered_sound);
                            - delay: 300ms
                      - voice_assistant.start:
                          wake_word: !lambda return wake_word;

voice_assistant:
  id: va
  microphone: nabu_mic_va
  media_player: nabu_media_player
  micro_wake_word: mww
  use_wake_word: false
  noise_suppression_level: 0
  auto_gain: 0 dbfs
  volume_multiplier: 1
  on_client_connected:
    - if:
        condition:
          - lambda: return id(init_in_progress);
          - switch.is_on: mic_mute_switch
        then:
          - switch.turn_off: mic_mute_switch
    - lambda: id(init_in_progress) = false;
    - micro_wake_word.start:
    - lambda: id(voice_assistant_phase) = ${voice_assist_idle_phase_id};
    - script.execute: control_leds
  on_client_disconnected:
    - voice_assistant.stop:
    - lambda: id(voice_assistant_phase) = ${voice_assist_not_ready_phase_id};
    - script.execute: control_leds
  on_error:
    - if:
        condition:
          and:
            - lambda: return !id(init_in_progress);
            - lambda: return code != "duplicate_wake_up_detected";
        then:
          - lambda: id(voice_assistant_phase) = ${voice_assist_error_phase_id};
          - script.execute: control_leds
  # When the voice assistant starts: Play a wake up sound, duck audio.
  on_start:
    - nabu.set_ducking:
        decibel_reduction: 20   # Number of dB quieter; higher implies more quiet, 0 implies full volume
        duration: 0.0s          # The duration of the transition (default is 0)
  on_listening:
    - lambda: id(voice_assistant_phase) = ${voice_assist_waiting_for_command_phase_id};
    - script.execute: control_leds
  on_stt_vad_start:
    - lambda: id(voice_assistant_phase) = ${voice_assist_listening_for_command_phase_id};
    - script.execute: control_leds
  on_stt_vad_end:
    - lambda: id(voice_assistant_phase) = ${voice_assist_thinking_phase_id};
    - script.execute: control_leds
  on_tts_start:
    - lambda: id(voice_assistant_phase) = ${voice_assist_replying_phase_id};
    - script.execute: control_leds
    # Start a script that would potentially enable the stop word if the response is longer than a second
    - script.execute: activate_stop_word_if_tts_step_is_long
  on_tts_end:
    - text_sensor.template.publish:
        id: tts_uri
        state: !lambda 'return x;'
    
  # When the voice assistant ends ...
  on_end:
    - wait_until:
        not:
          voice_assistant.is_running:
    # Stop ducking audio.
    - nabu.set_ducking:
        decibel_reduction: 0   # 0 dB means no reduction
        duration: 1.0s
    # Stop the script that would potentially enable the stop word if the response is longer than a second
    - script.stop: activate_stop_word_if_tts_step_is_long
    # Disable the stop word (If the tiemr is not ringing)
    - if:
        condition:
          switch.is_off: timer_ringing
        then:
          - lambda: id(stop).disable();
    # If the end happened because of an error, let the error phase on for a second
    - if:
        condition:
          lambda: return id(voice_assistant_phase) == ${voice_assist_error_phase_id};
        then:
          - delay: 1s
    # Reset the voice assistant phase id and reset the LED animations.
    - lambda: id(voice_assistant_phase) = ${voice_assist_idle_phase_id};
    - script.execute: control_leds
  on_timer_finished:
    - switch.turn_on: timer_ringing
    - lambda: |
        id(next_timer).publish_state(-1);
        id(next_timer_name).publish_state("-");
  on_timer_started:
    - script.execute: control_leds
    - lambda: |
        id(next_timer).publish_state(id(first_active_timer).seconds_left);
        id(next_timer_name).publish_state(id(first_active_timer).name);
  on_timer_cancelled:
    - script.execute: control_leds
    - lambda: |
        id(next_timer).publish_state(id(first_active_timer).seconds_left);
        id(next_timer_name).publish_state(id(first_active_timer).name);
  on_timer_updated:
    - script.execute: control_leds
    - lambda: |
        id(next_timer).publish_state(id(first_active_timer).seconds_left);
        id(next_timer_name).publish_state(id(first_active_timer).name);
  on_timer_tick:
    - script.execute: control_leds
    - lambda: | 
        int seconds_left = id(first_active_timer).seconds_left;
        if (std::abs(seconds_left) % 5 == 0) {
          id(next_timer).publish_state(seconds_left); 
        }

button:
  - platform: factory_reset
    id: factory_reset_button
    name: "Factory Reset"
    entity_category: diagnostic
    internal: true

debug:
  update_interval: 5s
